costastf/philips_hue_switch/images/IMG_20170518_141529.jpg

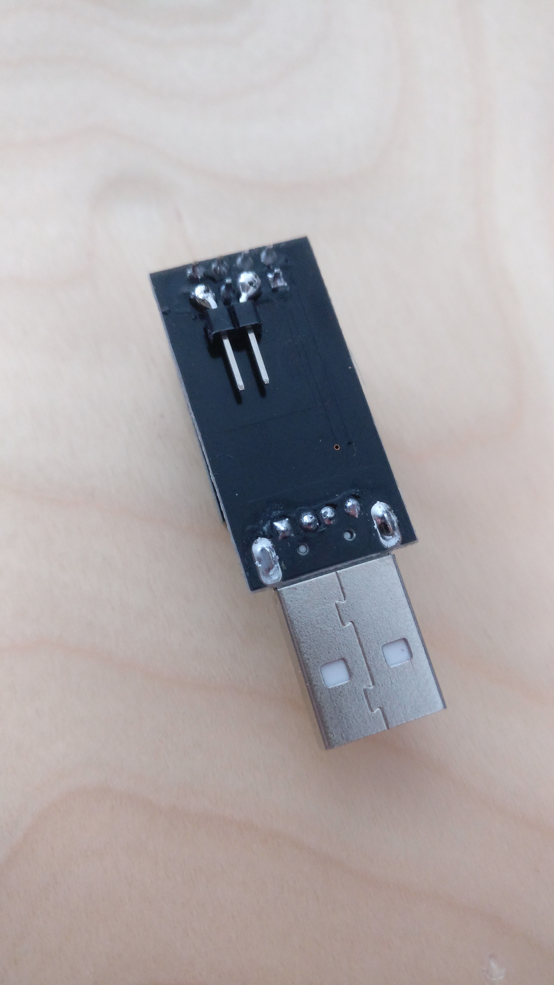
images/IMG_20170518_141529.jpg
