costastf/philips_hue_switch/images/IMG_20170518_165919.jpg

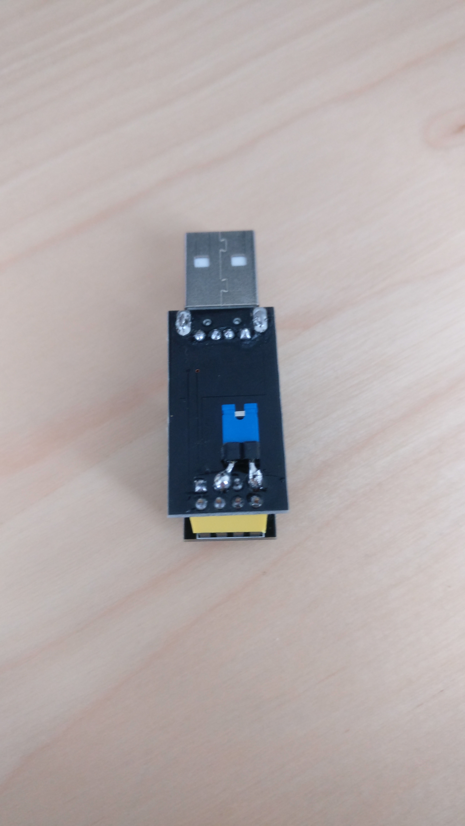
images/IMG_20170518_165919.jpg
