costastf/philips_hue_switch/images/IMG_20170519_095341.jpg

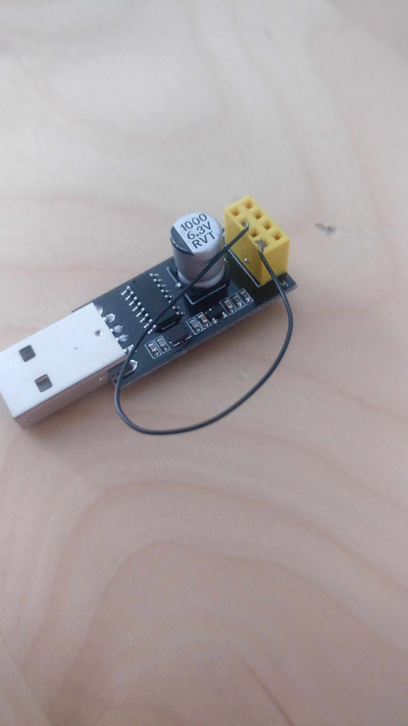
images/IMG_20170519_095341.jpg
