costastf/philips_hue_switch/images/IMG_20170522_201746.jpg

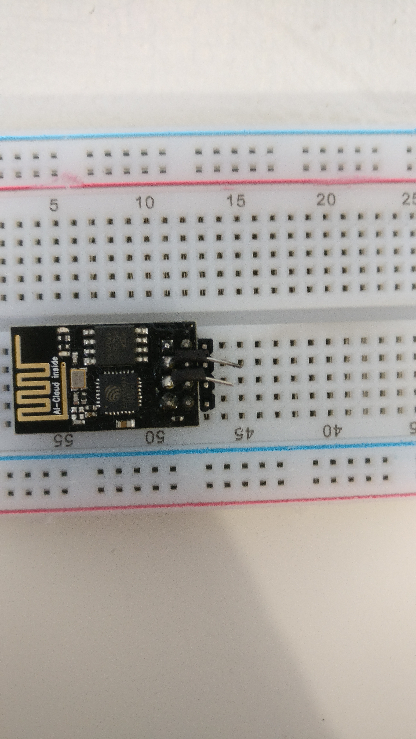
images/IMG_20170522_201746.jpg
