costastf/philips_hue_switch/images/IMG_20170522_202012.jpg

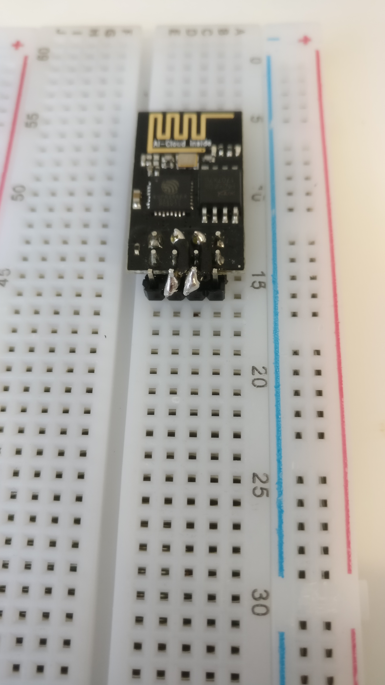
images/IMG_20170522_202012.jpg
