costastf/philips_hue_switch/images/IMG_20170522_202637.jpg

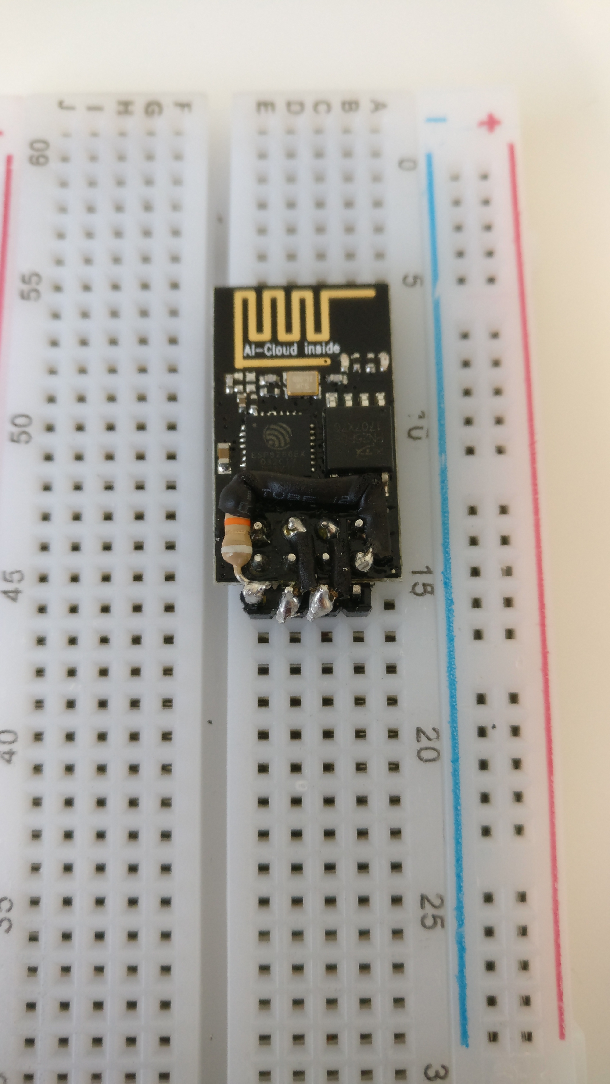
images/IMG_20170522_202637.jpg
