costastf/philips_hue_switch/images/IMG_20170522_203326.jpg

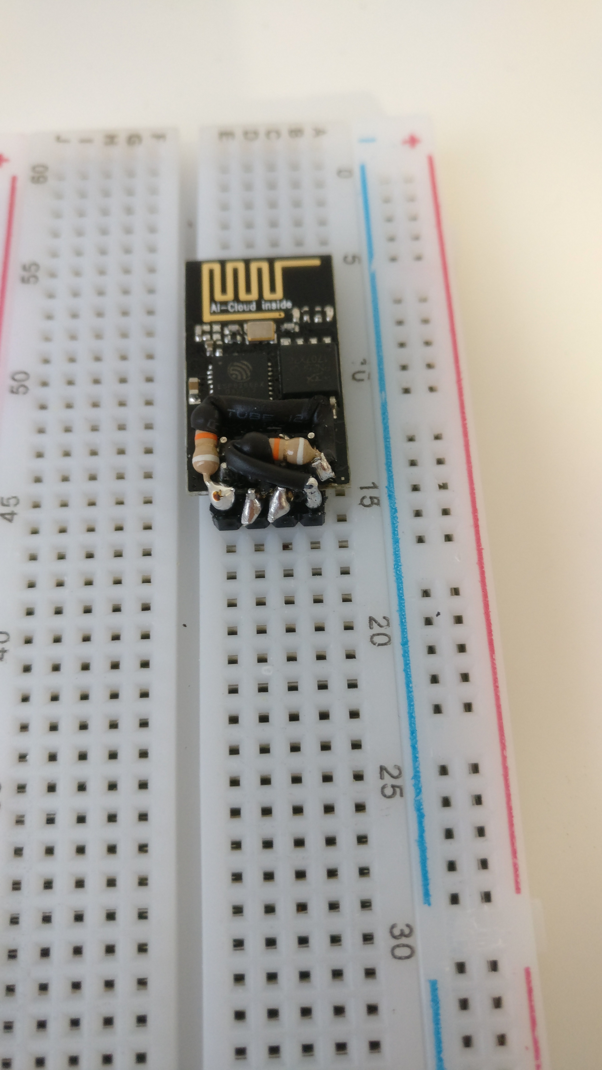
images/IMG_20170522_203326.jpg
