costastf/philips_hue_switch/images/IMG_20170522_203336.jpg

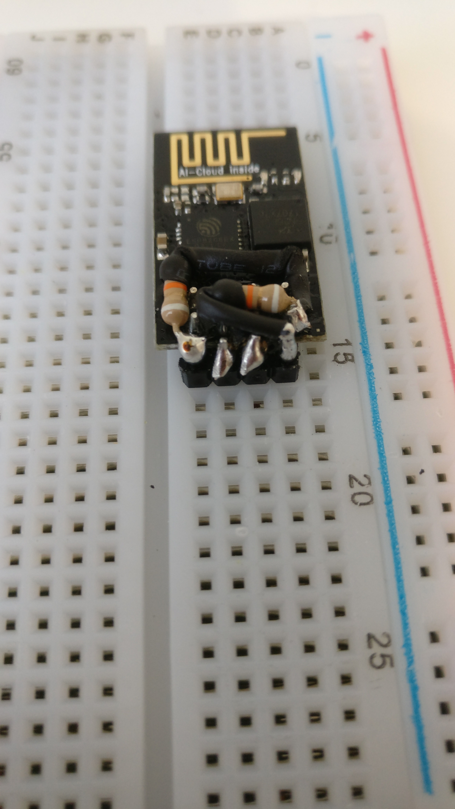
images/IMG_20170522_203336.jpg
