costastf/philips_hue_switch/images/IMG_20170522_210237.jpg

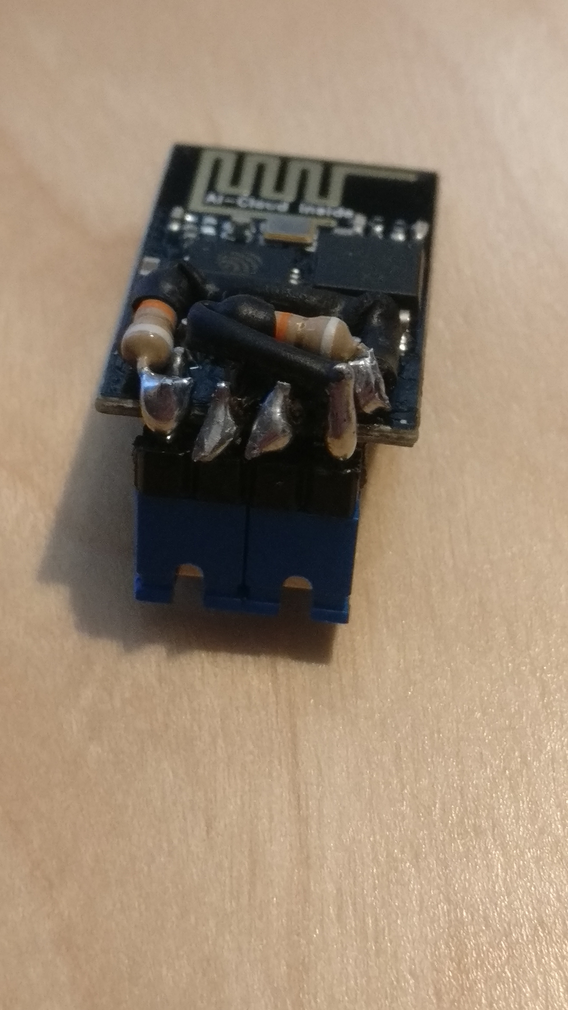
images/IMG_20170522_210237.jpg
